alexiaenache/Proiect_TSC/Images/image1.jpeg

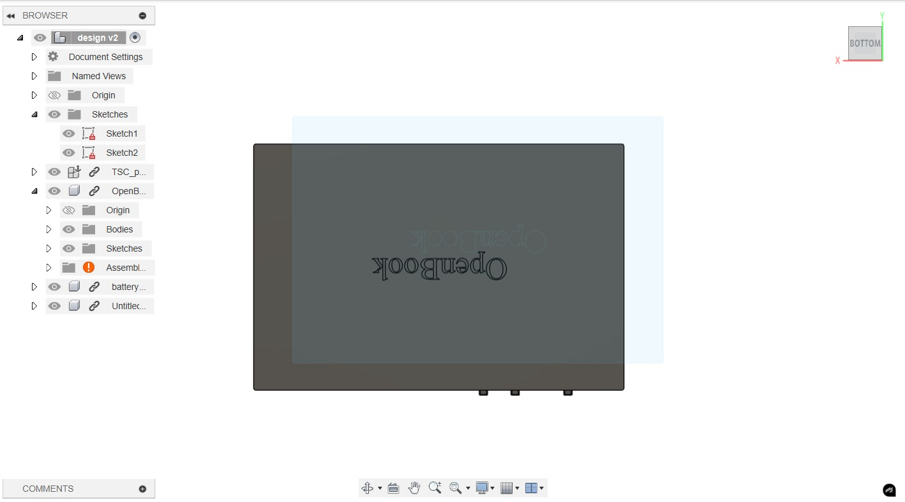
Images/image1.jpeg
